7901bill/carrier-board/Documentation/PCB-Audit-2026-10-09.md

# Saved PCB audit - 2026-10-09

Inspected `Hardware/Schematics & PCB/Watchdog PCB.PcbDoc` read-only. Embedded
save time: October 8, 2026, 11:34:26 PM. File size: 11,945,984 bytes.
SHA-256: `68eeec9831237657cf73e4daca9ceebf01d7ab81fae351649f8a07e9a41950d0`.

## Conclusion

Routing is substantially implemented, consistent with a finishing phase.
All nine pair definitions exist and both members of every pair have tracks
on the top copper layer with no pair-net vias. This confirms progress since
the October 5 no-pair-object snapshot; it does not prove complete connectivity,
correct impedance, or DRC sign-off.

## Saved-file evidence

| Item | Finding |
|---|---|
| Components / nets / pads | 43 / 51 / 433 |
| Track records | 1,461 total; 756 net-assigned copper tracks: 535 top and 221 bottom |
| Vias | 105 total; 57 GND, 14 `5V`, 34 on other nets |
| Pair definitions | PCIe TX/RX/CLK; CAM D0/D1/D2/D3/CLK; USB |
| Saved connections | 85 records: 83 GND, two `NetCN1_78` |
| Saved polygons | Two split-plane records: PLANE1 GND and PLANE2 `5V`; no top/bottom polygon records in `Polygons6` |
| Outline | Four straight corners, approximately 100.03 x 60.03 mm |
| Nearest GND via to each outline corner | Approximately 19.94, 6.15, 22.69, and 11.50 mm, in saved vertex order |
| DRC evidence | No saved DRC report found in the project |

Corner vias and the proposed outline revision are still finishing work.
Internal plane records already exist; polygon work should not be described
as starting from a board with no plane definitions. Refresh/re-pour in Altium
and inspect actual connectivity and copper islands.

## Differential routing checks still open

The highest-priority enabled differential routing rule is `USB_DiffPair`,
with `SCOPE1EXPRESSION=All`, a profile-driven 90-ohm target, 5 mil gap, and
10.2498 mil preferred top-layer width. A lower-priority generic rule is also
scoped to `All` and retains 15 mil width / 10 mil gap. A rule's name does not
restrict its scope. Confirm effective application and provide the required
100-ohm MIPI routing rule/profile rather than treating nine pair definitions
as impedance sign-off.

Summed straight-track geometry (excluding pad lengths and electrical delay):

| Pair | Positive / negative track length (mm) |
|---|---|
| PCIE_TX | 54.019 / 54.019 |
| PCIE_RX | 54.134 / 54.134 |
| PCIE_CLK | 54.312 / 54.312 |
| CAM_D3 | 17.840 / 17.840 |
| CAM_D2 | 17.757 / 17.757 |
| CAM_D1 | 17.762 / 17.762 |
| CAM_D0 | 17.886 / 17.888 |
| CAM_CLK | 17.638 / 17.638 |
| USB | 34.372 / 31.336 |

USB has approximately 3.04 mm difference in saved track geometry. Review
actual pad-to-pad/electrical lengths and the applicable skew rule in Altium;
this is a review finding, not a demonstrated specification failure.

## Method and limits

Read OLE compound-file streams using Python `olefile`; inspect length-prefixed
property records and track/via/connection records. Check stream header counts
and net assignments. Binary field interpretation was cross-checked against
[KiCad's Altium parser](https://docs.kicad.org/doxygen/altium__parser__pcb_8cpp_source.html).
The saved ECO log at October 8, 11:19:12 PM also records creation of the eight
PCIe/camera pair objects; the PCB itself contains those plus USB.

No CAD edits, Altium DRC run, full copper connectivity calculation, impedance
simulation, or live unsaved-session inspection occurred. Saved connection
records may need regeneration and are not a current violation count. Earlier
schematic/footprint findings were not re-audited or closed in this pass.

## Next work

Add corner GND vias; revise the outline; add/re-pour polygon copper; refresh
connectivity and inspect `NetCN1_78` and GND; verify differential rule scopes
and USB skew; resolve remaining violations and save a final Altium DRC report.
Complete mechanical, electrical, BOM/CPL, and output review before release.
